KarlOttoFuchs/ShellyBluRelay/_bmad-output/planning-artifacts/implementation-readiness-report-2026-01-14.md

---
stepsCompleted: [1, 2, 3, 4, 5, 6]
documentInventory:
  prd: '/Users/karlfuchs/Documents/Development/Projects/ESP32C3 Relay Module/_bmad-output/planning-artifacts/prd.md'
  architecture: '/Users/karlfuchs/Documents/Development/Projects/ESP32C3 Relay Module/_bmad-output/planning-artifacts/architecture.md'
  epics: null
  ux: null
project_name: 'ESP32C3 Relay Module'
user_name: 'Karl'
date: '2026-01-14'
totalFRs: 56
totalNFRs: 23
readinessStatus: 'READY_TO_PROCEED'
criticalIssues: 1
recommendedActions: 2
---

# Implementation Readiness Assessment Report

**Date:** 2026-01-14
**Project:** ESP32C3 Relay Module

## Document Inventory

### Documents Found and Validated

**PRD (Product Requirements Document):**
- File: prd.md
- Size: 64K
- Last Modified: Jan 13 22:25
- Status: ✅ Found

**Architecture Document:**
- File: architecture.md
- Size: 51K
- Last Modified: Jan 14 07:10
- Status: ✅ Found

**Epics & Stories:**
- Status: ⚠️ Not yet created (expected - Phase 3 validating readiness for Phase 4)

**UX Design:**
- Status: ⚠️ Not created (conditional per workflow status)

### Assessment Scope

This Implementation Readiness Review will focus on:
1. PRD completeness and quality
2. Architecture completeness and alignment with PRD
3. Readiness to proceed to Epic & Story creation

Since Epics & Stories have not been created yet, this is the appropriate validation point before Phase 4 implementation planning begins.

## PRD Analysis

### Functional Requirements Extracted

**Total FRs: 56**

**Hardware Interface & Validation (FR1-FR6):**
- FR1: System can control relay (energize/de-energize) via GPIO output
- FR2: System can detect button press via GPIO input for triggering configuration mode
- FR3: White status LED can indicate operating mode (fast blink = configuration mode, slow blink = listening mode, solid ON = relay energized)
- FR4: Red error LED can indicate diagnostic states (single blink = sensor not detected 24h, double blink = NVS failure, triple blink = BLE initialization failure)
- FR5: System can communicate via USB serial connection for configuration and status reporting
- FR6: System can operate from either USB-C 5V power OR external DC 12-24V power, with Schottky diode isolation preventing backfeeding when both sources connected

**BLE Sensor Communication (FR7-FR11):**
- FR7: System can receive and decode BLE advertising packets from supported sensors without establishing connections
- FR8: System can decode sensor events from Shelly BLU Button (single/double/triple press), Motion (motion detected), and Door/Window (open/close) devices
- FR9: System can extract device MAC address, event type, battery level, and RSSI from BLE advertising packets
- FR10: System can filter BLE packets to only process events from registered sensor MAC address
- FR11: System can detect when registered sensor has not been seen for 24 hours and alert user

**Sensor Registration & Configuration (FR12-FR16):**
- FR12: System can enter 30-second sensor learning mode when physical button pressed, auto-registering first sensor that triggers during window
- FR13: Users can manually register sensor by MAC address when trigger-based learning fails
- FR14: System can store single sensor configuration persistently in NVS (survives power cycles)
- FR15: Users can clear registered sensor configuration
- FR16: System can validate sensor MAC address format before registration

**Relay Control & Timer Logic (FR17-FR21):**
- FR17: System can energize relay when registered sensor triggers event
- FR18: System can de-energize relay automatically after configurable timer expires (1-600 seconds)
- FR19: Users can configure relay-on duration (timer setting) with 1-second granularity
- FR20: System can support two retriggering modes: "extend" (reset timer on new trigger) or "ignore" (ignore triggers while relay active)
- FR21: System can maintain relay state and timer configuration across power cycles

**Event Logging & Diagnostics (FR22-FR26):**
- FR22: System can buffer last 10 trigger events with timestamps (uptime-based acceptable for MVP)
- FR23: Users can retrieve event log showing trigger history
- FR24: System can log errors (NVS failures, BLE initialization failures, sensor timeouts)
- FR25: Users can retrieve error log for troubleshooting
- FR26: Users can query comprehensive system status including current state, sensor info (MAC, last seen, RSSI), relay state, timer value, event count, error conditions

**CLI Configuration Interface (FR27-FR32):**
- FR27: CLI can auto-detect ESP32-C3 serial port on common platforms (Windows, macOS, Linux) with manual selection fallback when multiple ports detected
- FR28: CLI can communicate with firmware using text-based serial protocol (115200 baud, newline-terminated commands, JSON responses, defined error codes)
- FR29: CLI can display colorful, formatted output using tables, progress indicators, and color-coded status (green success, yellow warnings, red errors)
- FR30: CLI can provide comprehensive help text auto-generated from command documentation
- FR31: CLI can provide clear, actionable error messages for connection failures and configuration issues
- FR32: Users can test relay manually (turn ON/OFF) via CLI command

**State Machine & Safety (FR33-FR38):**
- FR33: System can transition between Configuration, Listening, and Active states based on sensor registration, trigger events, and timer expiration
- FR34: System can default relay to OFF state on boot, error conditions, or power loss (fail-safe)
- FR35: System can validate configuration changes (timer range 1-600 seconds, retrigger mode enum validation) before applying
- FR36: System can recover from firmware crashes with serial crash logs including stack traces
- FR37: System can implement watchdog timer that resets MCU if firmware hangs, with relay defaulting to OFF on reset
- FR38: System can detect NVS corruption and prevent relay activation with corrupted configuration

**Firmware Management & Updates (FR39-FR41):**
- FR39: Users can update firmware via standard ESP-IDF flashing tools over USB serial
- FR40: System can maintain firmware version information accessible via status command
- FR41: Firmware can log boot reason (power-on, watchdog reset, crash) for diagnostics

**Documentation & Extensibility (FR42-FR46):**
- FR42: Firmware codebase can achieve 4.0/5.0 readability rating from independent developers
- FR43: Architecture documentation can include state machine diagram, serial protocol specification, and NVS schema
- FR44: Extension guide can provide clear instructions for adding support for new sensor types
- FR45: Code can include inline comments explaining non-obvious design decisions, BTHome packet format details, and state transition logic
- FR46: CLI can provide auto-generated help text with examples and argument constraints for every command

**Future Capabilities - Post-MVP (FR47-FR56):**
- FR47: System can support 2-5 registered sensors triggering same relay (V1.1)
- FR48: Users can export configuration to YAML file (V1.2)
- FR49: Users can import configuration from YAML file with schema validation (V1.2)
- FR50: Users can scan and select sensors from list of nearby BLE devices (V1.2)
- FR51: CLI can wrap esptool functionality for simplified firmware flashing (V1.2)
- FR52: System can support lux gate triggering (only activate relay below light threshold) (V1.3)
- FR53: Users can send AT-style commands directly via serial terminal without CLI (V1.3)
- FR54: Users can execute factory reset to clear all NVS data and return to defaults (V1.3)
- FR55: System can support OTA firmware updates over BLE (V2.0+)
- FR56: Users can configure system via mobile BLE app without USB connection (V2.0+)

### Non-Functional Requirements Extracted

**Total NFRs: 23**

**Performance (NFP1-NFP5):**
- NFP1: Relay must energize within 500ms of BLE event detection
- NFP2: Relay countdown timer must be accurate within ±1 second over 10-minute duration
- NFP3: System must process BLE advertising packets at scan rate of 10 packets/second minimum
- NFP4: CLI status command must return results within 2 seconds on USB serial connection
- NFP5: System must complete boot and enter Listening state within 5 seconds of power-on

**Reliability (NFR1-NFR5):**
- NFR1: Relay MUST default to OFF state in 100% of error conditions
- NFR2: Watchdog timer must reset MCU within 10 seconds if firmware hangs; relay must de-energize within 1 second of watchdog reset
- NFR3: Configuration writes to NVS must survive 10,000 power cycle events with <0.1% corruption rate
- NFR4: System must detect and process BLE sensor events with >95% success rate at RSSI ≥ -70 dBm
- NFR5: System must operate continuously for 168 hours without firmware crash or memory leak

**Usability (NFU1-NFU5):**
- NFU1: 80% of first-time users must successfully register sensor and test relay within 10 minutes
- NFU2: 100% of error messages must include actionable guidance
- NFU3: Status command must answer: relay state, sensor registered, sensor in range, timer setting, errors - without additional commands
- NFU4: Every CLI command must have auto-generated help text with description, argument constraints, and usage example
- NFU5: Users must be able to distinguish operating modes via LED patterns without documentation (>90% accuracy)

**Maintainability (NFM1-NFM4):**
- NFM1: Firmware codebase must achieve ≥4.0/5.0 readability rating from 3+ independent developers
- NFM2: Architecture documentation must include state machine diagram, serial protocol spec, NVS schema
- NFM3: Intermediate developers must be able to add support for new sensor type in ≤4 hours
- NFM4: Non-obvious code sections must have explanatory comments (BTHome parsing, state transitions, NVS validation, watchdog config)

**Compatibility (NFC1-NFC5):**
- NFC1: CLI must run on Windows 10+, macOS 11+, Linux (Ubuntu 20.04+) without platform-specific code paths
- NFC2: CLI must correctly identify ESP32-C3 USB-UART bridges (CP2102, CH340) with manual selection fallback
- NFC3: Firmware must compile and run on ESP-IDF 5.1.x LTS and 5.2.x
- NFC4: System must correctly parse BTHome v2 packets from Shelly BLU Button, Motion, and Door/Window sensors
- NFC5: CLI must run on Python 3.8+

### Additional Requirements & Constraints

**Technical Architecture Requirements:**
- **Dual-Stack System**: ESP32-C3 firmware (C/ESP-IDF) + Python CLI (Typer/Rich)
- **Serial Protocol**: Text-based, 115200 baud, newline-terminated, JSON responses
- **BTHome v2 Protocol**: Passive listener (no sensor connections), supports Button/Motion/Door sensors
- **Power Architecture**: Dual input with Schottky diodes (USB-C 5V OR DC 12-24V)
- **Security Model**: Fail-safe defaults, MAC filtering, no remote access in MVP

**Project Constraints:**
- **ONE Sensor Maximum**: Enforced in MVP firmware and CLI
- **Hardware Validation First**: Priority #0 - gates all architectural work
- **Development Timeline**: 4-6 weeks for MVP
- **Code Quality Target**: 4.0/5.0 readability for educational transparency

**Success Criteria (MVP Must-Pass):**
1. Hardware validation complete
2. End-to-end working (one BLU sensor triggers relay)
3. 2-minute first success achieved
4. Self-diagnosable via status command
5. Zero stuck-on relay incidents across 100+ test cycles
6. Code clarity confirmed (3+ developers rate >4/5)
7. Foundation supports multi-sensor V1.1 without major refactoring

### PRD Completeness Assessment

**Strengths:**
✅ Comprehensive requirements coverage (56 FRs + 23 NFRs)
✅ Clear user journeys with edge cases (Marcus, Sofia, Priya)
✅ Detailed technical architecture specifications
✅ Well-defined success criteria with measurable outcomes
✅ Safety-critical requirements explicitly documented (NFR1, FR34, FR37)
✅ Phased roadmap with clear MVP scope boundaries
✅ Educational transparency requirements well-articulated

**Identified Issues:**
⚠️ **FR11 Flaw Identified in Architecture Review**: 24-hour sensor timeout is problematic (vacation scenario - sensor may not trigger for weeks). Architecture document corrected this to battery-based monitoring instead.

**PRD Corrections Required** (per Architecture document findings):
1. Remove FR11: "System can detect when registered sensor has not been seen for 24 hours"
2. Update FR21 partially: Remove 24-hour timeout language, keep battery monitoring
3. Update NFR4: Remove 24-hour detection reference
4. Add battery-based health monitoring: Track battery % from BTHome packets, warn at <20%, error at <10%

**Overall Completeness**: EXCELLENT - PRD is comprehensive and implementation-ready, pending minor corrections identified during architectural design phase.

## Epic Coverage Validation

### Epics Document Status

**Status**: ❌ NOT FOUND

The Epics & Stories document has not been created yet. This is expected at this stage of the workflow - we are validating PRD and Architecture readiness BEFORE Epic creation begins.

### Coverage Analysis

**Cannot perform FR coverage validation** - no epics exist to validate against.

**Next Step Required**: Create Epics & Stories document based on:
1. All 56 Functional Requirements from PRD
2. Architectural decisions and implementation patterns from Architecture document
3. User journeys (Marcus, Sofia, Priya) from PRD
4. Non-functional requirements that affect epic implementation

### Recommendation

**PROCEED TO EPIC CREATION** using:
- Workflow: `/bmad:bmm:workflows:create-epics-and-stories`
- Inputs: PRD + Architecture (both validated and ready)
- Expected Output: Epics & Stories with complete FR coverage

**Note**: This Implementation Readiness Review will resume AFTER epics are created to validate coverage completeness.

## UX Alignment Assessment

### UX Document Status

**Status**: ❌ NOT FOUND (Conditional - not required for this project type)

### Project Type Analysis

This project is a **dual-stack IoT/Embedded + CLI tool** system:
- **Firmware**: ESP32-C3 embedded system (no UI)
- **CLI Tool**: Python command-line interface using Typer + Rich for terminal output

### UX Requirements in PRD

The PRD **DOES include comprehensive UX requirements** for the CLI tool:

**CLI User Experience Requirements Identified in PRD:**
1. **NFU1**: 80% of first-time users must successfully register sensor within 10 minutes
2. **NFU2**: 100% of error messages must include actionable guidance
3. **NFU3**: Status command must answer all diagnostic questions without additional commands
4. **NFU4**: Every CLI command must have auto-generated help text
5. **NFU5**: LED feedback patterns must be distinguishable without documentation

**CLI Design Specifications in PRD:**
- FR29: Colorful formatted output using tables, progress indicators, color-coded status
- FR30: Comprehensive help text auto-generated from command documentation
- FR31: Clear, actionable error messages
- Output examples showing Rich table formatting with color schemes

**User Journey Validation:**
- Marcus's journey: Demonstrates CLI usability flow (auto-port detection, simple commands, RSSI troubleshooting)
- Sofia's journey: Demonstrates installer workflow (config import/export in V1.2)
- Priya's journey: Demonstrates learning-oriented CLI design

### UX ↔ Architecture Alignment

**Architecture Document Addresses UX Requirements:**

✅ **Serial Protocol** (Decision 1): Defines CLI↔firmware communication contract
✅ **Error Handling** (Decision 5): CLI error presentation with Rich formatting specified
✅ **Logging & Diagnostics** (Decision 6): CLI status command output with Rich table design
✅ **Implementation Patterns**: CLI naming conventions, output formatting, error handling patterns all defined

**Alignment Examples:**
- Architecture specifies exact Rich table format for status command (matches PRD FR29)
- Error codes defined in serial protocol align with actionable CLI messages (matches NFU2)
- RSSI color-coding thresholds documented (supports Marcus's troubleshooting workflow)

### Alignment Assessment

**Status**: ✅ EXCELLENT ALIGNMENT

**Rationale**:
- CLI UX requirements comprehensively documented in PRD (not in separate UX document)
- Architecture document fully addresses CLI design with implementation patterns
- No traditional GUI/web UX needed - command-line interface appropriate for target users
- User journeys validate CLI usability through realistic scenarios

**No UX Document Needed Because:**
1. CLI tool has different UX paradigm than web/mobile apps (no visual mockups needed)
2. UX requirements embedded in PRD functional requirements and user journeys
3. Architecture patterns specify terminal output formatting (Rich library)
4. Target users (DIY enthusiasts, installers, developers) comfortable with CLI interfaces

### Warnings

⚠️ **NONE** - No separate UX document needed for CLI tool. All user experience requirements adequately captured in PRD and addressed in Architecture.

### Recommendation

**No Action Required** - Proceed with Epic creation. CLI UX requirements will be traced through epics via PRD FR coverage.

## Epic Quality Review

### Epics Document Status

**Status**: ❌ NOT FOUND

The Epics & Stories document has not been created yet. Cannot perform epic quality review without epics.

### Quality Review Deferral

**Best Practices Validation**: DEFERRED until epics are created

**When epics are created, the following validations must be performed:**

#### Epic Structure Validation
- ✅ Epic titles must be user-centric (what user can do)
- ✅ Epics must deliver standalone user value (not technical milestones)
- ✅ Each epic can function independently using only previous epic outputs
- ❌ FORBIDDEN: "Setup Database", "API Development", "Infrastructure Setup" as epic titles

#### Story Quality Requirements
- ✅ Clear user value in each story
- ✅ Stories independently completable
- ✅ No forward dependencies (Story 1.2 cannot depend on Story 1.4)
- ✅ Acceptance criteria in Given/When/Then format
- ✅ Database tables created only when first needed (not upfront)

#### Critical Checks for This Project
1. **Starter Template**: Architecture specifies standard ESP-IDF + Python initialization (no template)
   - Epic 1 Story 1 should initialize both firmware and CLI projects
2. **Greenfield Project**: Must include project setup, dev environment, CI/CD stories
3. **Dual-Stack Complexity**: Stories must account for firmware + CLI coordination

### Recommendation

After Epic creation, run this quality review to validate:
- All 56 FRs traced to stories
- No technical epics (hardware validation, BTHome parser, NVS storage as epics = WRONG)
- User value focus (sensor registration, relay control, CLI commands as epics = RIGHT)
- Independence verified (Epic 2 doesn't need Epic 3 to work)

## Summary and Recommendations

### Overall Readiness Status

**STATUS: ✅ READY TO PROCEED** (with minor PRD corrections)

**Assessment Context**: This review evaluated PRD and Architecture documents only, as Epics & Stories have not yet been created. This is the appropriate validation point before Epic creation begins.

### Critical Issues Requiring Immediate Action

**1. PRD Corrections - FR11 (24-Hour Sensor Timeout Flaw)**
- **Issue**: FR11 specifies "System can detect when registered sensor has not been seen for 24 hours" which is flawed for vacation scenarios (sensor may not trigger for weeks)
- **Impact**: MEDIUM - Affects FR11, partial FR21, NFR4
- **Resolution**: Architecture document already corrected this to battery-based monitoring (<20% warning, <10% error)
- **Action Required**: Update PRD to remove FR11 and replace with battery-based health monitoring specification

### Strengths Identified

**PRD Quality - EXCELLENT:**
✅ 56 comprehensive functional requirements covering all MVP features
✅ 23 non-functional requirements with measurable criteria
✅ Clear user journeys with edge cases (Marcus, Sofia, Priya)
✅ Safety-critical requirements explicitly documented (NFR1, FR34, FR37)
✅ Phased roadmap with clear MVP scope boundaries
✅ Educational transparency requirements well-articulated

**Architecture Quality - EXCELLENT:**
✅ All 6 critical architectural decisions made collaboratively
✅ Complete implementation patterns to prevent AI agent conflicts
✅ Serial protocol, state machine, NVS schema fully specified
✅ Error handling patterns ensure fail-safe relay behavior
✅ PRD flaw identified and corrected during architecture design

**PRD ↔ Architecture Alignment - EXCELLENT:**
✅ Architecture addresses all PRD FRs through 6 architectural decisions
✅ Implementation patterns support all NFRs (performance, reliability, usability)
✅ CLI UX requirements comprehensively addressed (Rich formatting, error handling)
✅ Safety requirements encoded in patterns (relay_force_off() mandatory)

### Recommended Next Steps

**1. Update PRD (Optional - Minor Corrections):**
   - Remove FR11: "24-hour sensor timeout detection"
   - Update FR21 partially: Remove timeout language, emphasize battery monitoring
   - Update NFR4: Remove 24-hour detection reference
   - Add explicit battery monitoring requirement: Warn at <20%, error at <10%
   - **Time Estimate**: 15-30 minutes
   - **Priority**: LOW (Architecture already has correct specification)

**2. Create Epics & Stories (Required - Next Phase):**
   - Workflow: `/bmad:bmm:workflows:create-epics-and-stories`
   - Inputs: PRD (56 FRs) + Architecture (6 decisions + patterns)
   - Expected Output: User-value focused epics with complete FR coverage
   - **Critical**: Ensure epics deliver user value (NOT "Setup Database", "Build API")
   - **Critical**: Verify no forward dependencies (Story 1.2 cannot depend on Story 1.4)
   - **Time Estimate**: 2-4 hours for comprehensive epic planning

**3. Run Implementation Readiness Review Again (After Epic Creation):**
   - Re-run this workflow to validate FR coverage completeness
   - Validate epic quality against best practices
   - Verify story acceptance criteria completeness
   - Ensure implementation readiness before Phase 4

### Documents Ready for Epic Creation

**✅ PRD**: Complete with minor flaw corrected in Architecture
**✅ Architecture**: Complete with all decisions and patterns defined
**❌ Epics & Stories**: Not yet created (next step)
**N/A UX Design**: Not required (CLI tool - UX embedded in PRD)

### Final Note

This assessment reviewed **2 of 3** planning artifacts (PRD + Architecture). The documents are **implementation-ready** with one minor PRD correction recommended (but not blocking).

**Key Finding**: Architecture review caught a significant requirements flaw (24-hour timeout) and corrected it before implementation - demonstrating the value of architectural analysis.

**Recommendation**: Proceed directly to Epic & Story creation. The PRD correction can be addressed later as it does not block Epic planning (Architecture has the correct specification).

**Next Workflow**: `/bmad:bmm:workflows:create-epics-and-stories`

---

**Assessment Date**: 2026-01-14  
**Assessor**: Implementation Readiness Review Workflow  
**Project**: ESP32C3 Relay Module  
**Phase**: 3 (Solutioning) → Ready for Phase 4 (Implementation Planning)
